ThePurpleOne/volumer/pcb/volumer_v1.0/qr.png

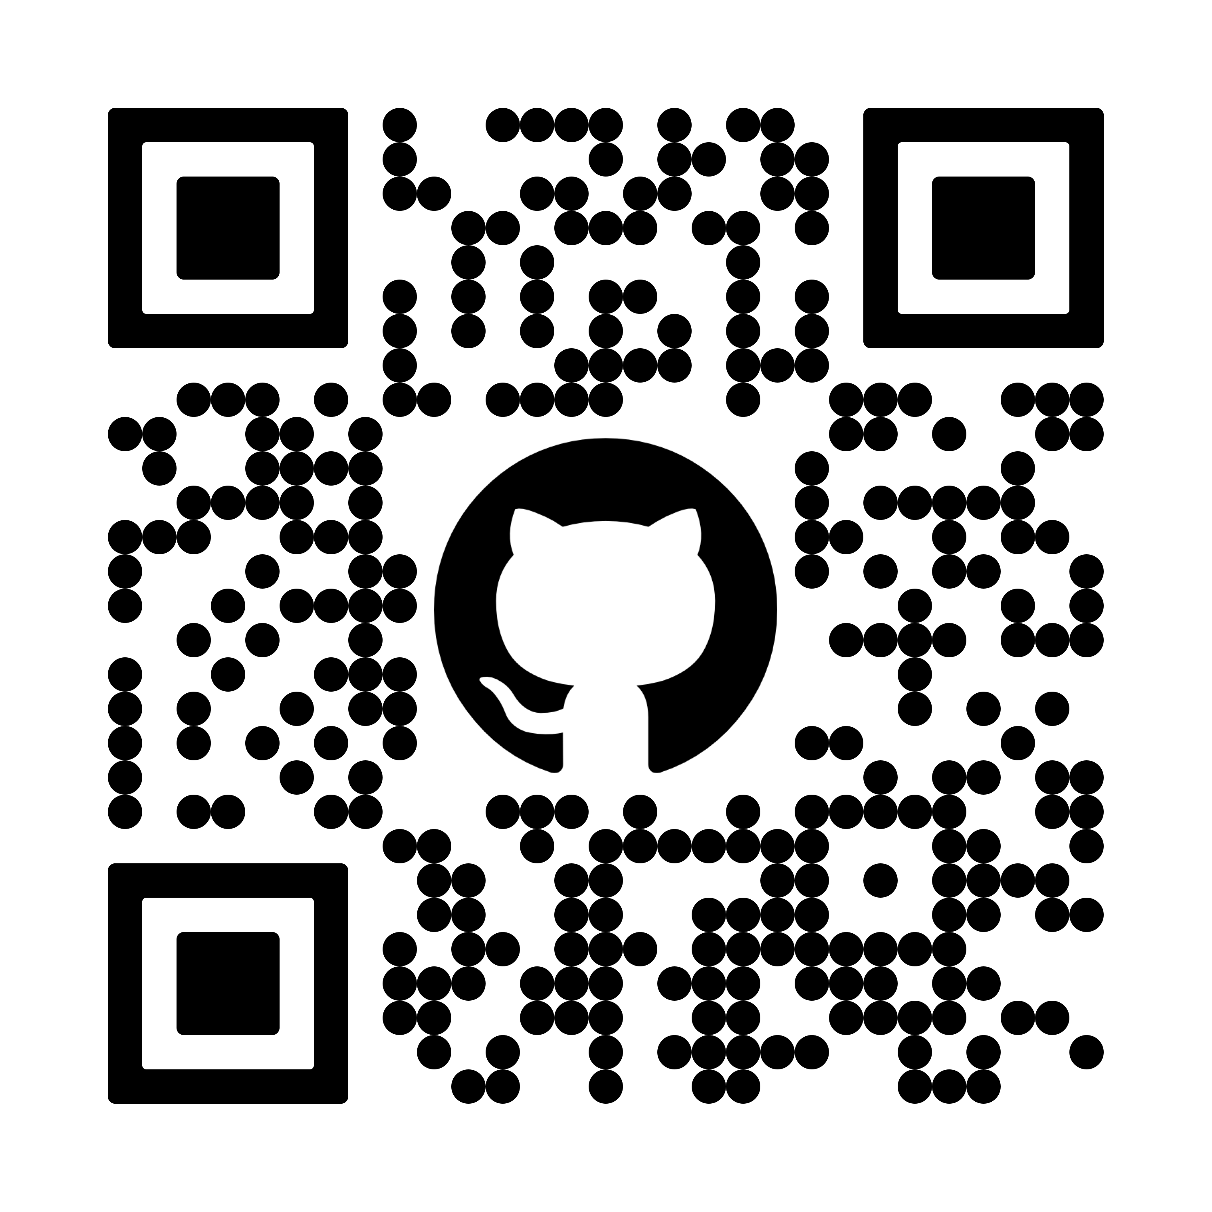
pcb/volumer_v1.0/qr.png
